omiagut/wifiRelay/pictures/p01.jpg

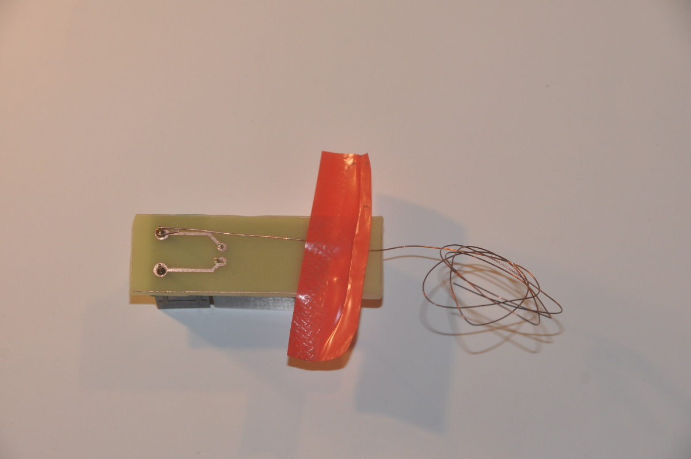
pictures/p01.jpg
