omiagut/wifiRelay/pictures/p04.jpg

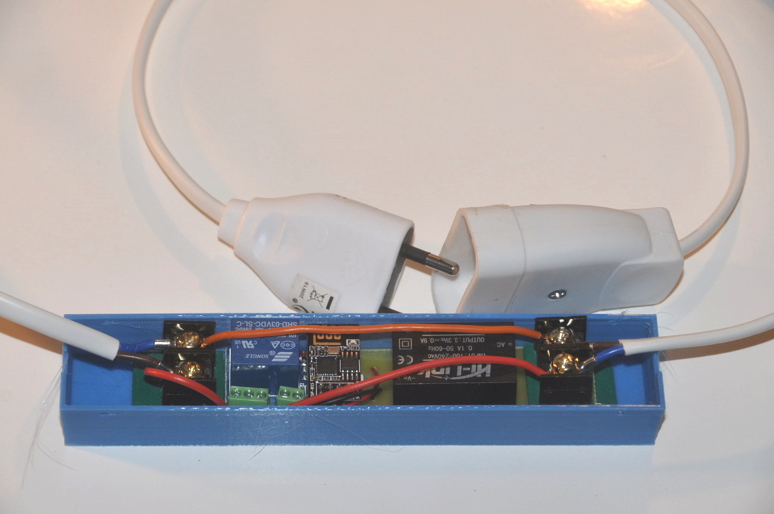
pictures/p04.jpg
