omiagut/wifiRelay/pictures/p05.jpg

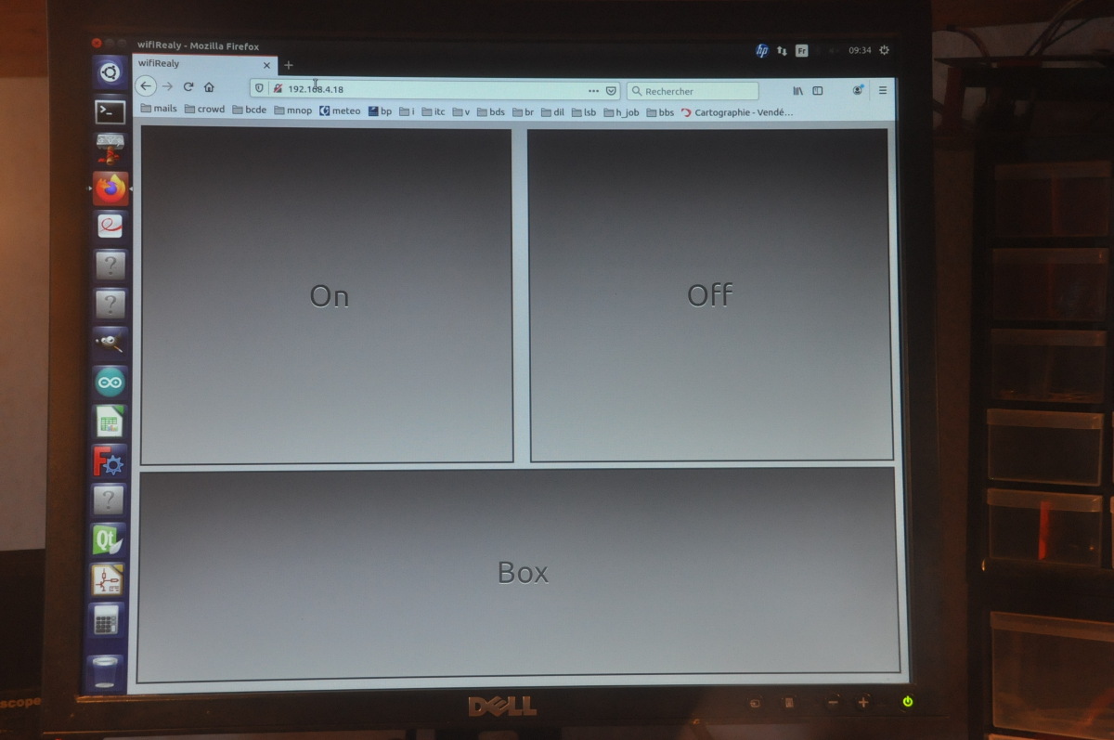
pictures/p05.jpg
